NguyennQuangMinh/ESP32_C3_RF/Documents/Images/SYSTEM_BLOCK.png

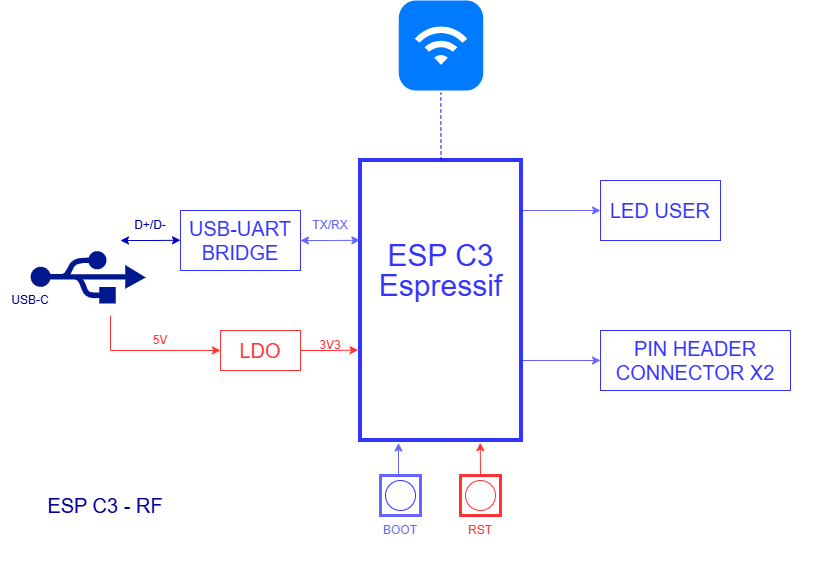
Documents/Images/SYSTEM_BLOCK.png
