NguyennQuangMinh/ESP32_C3_RF/Documents/TMP/W25Q32JVSSIQ/Altium/W25Q32JVSSIQ/SOIC-8_5P28X5P28_WIN.step

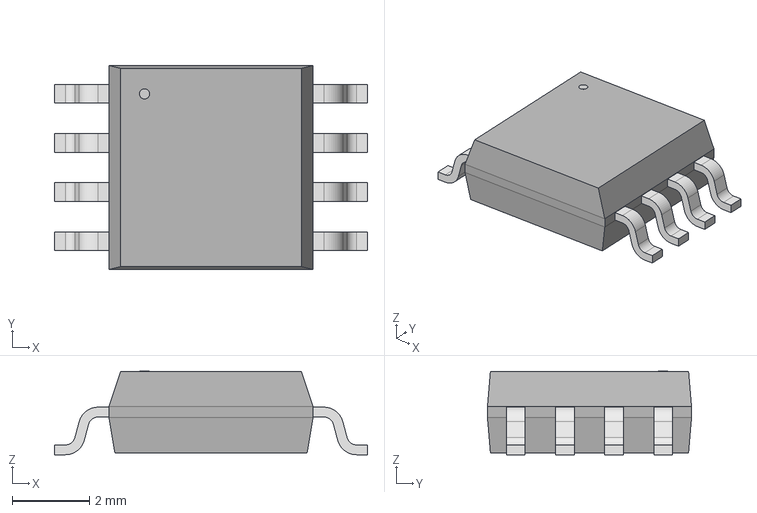
[picture p33: CAD file, 2026-04-23]
Documents/TMP/W25Q32JVSSIQ/Altium/W25Q32JVSSIQ/SOIC-8_5P28X5P28_WIN.step
8.10 x 5.28 x 2.16 mm
