NguyennQuangMinh/ESP32_C3_RF/Documents/TMP/3D Body/C0402C152J5GACTU.STEP

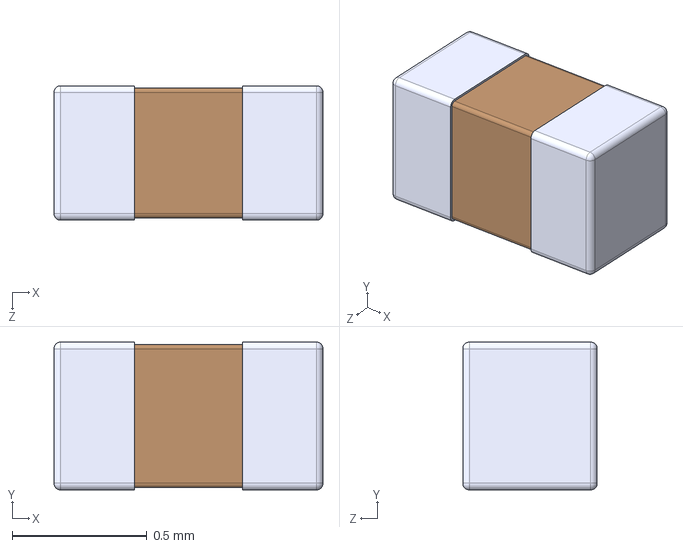
[picture p34: CAD file, 2026-04-23]
Documents/TMP/3D Body/C0402C152J5GACTU.STEP
1.00 x 0.55 x 0.5 mm
