NguyennQuangMinh/ESP32_C3_RF/Documents/TMP/3D Body/SS8050-G--3DModel-STEP-1.STEP

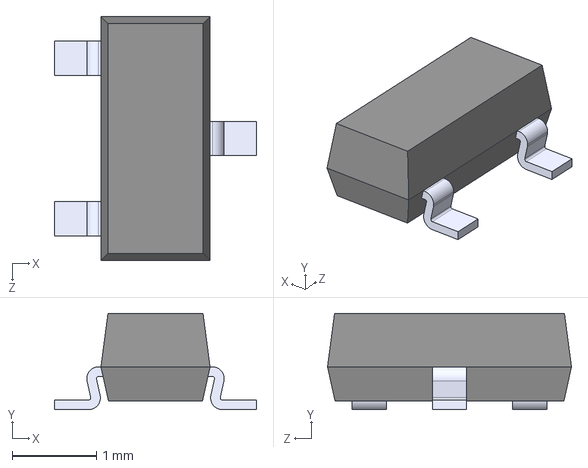
[picture p35: CAD file, 2026-04-23]
Documents/TMP/3D Body/SS8050-G--3DModel-STEP-1.STEP
2.40 x 1.14 x 2.90 mm
